inpudiy/KOMETA/IMAGE/GALLERY/blue.webp

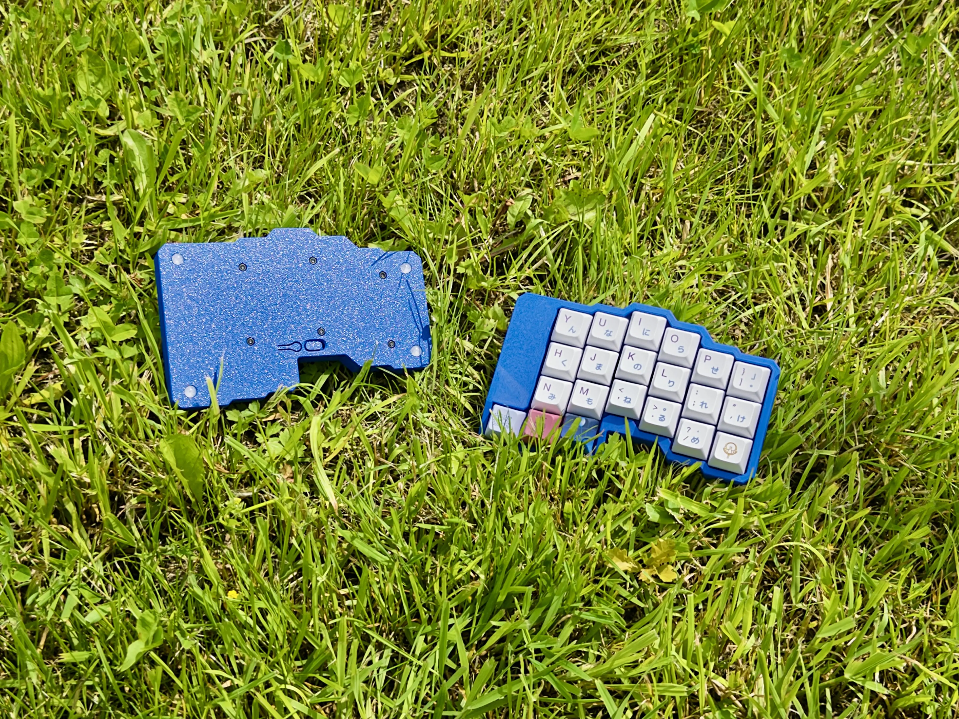
IMAGE/GALLERY/blue.webp
