inpudiy/KOMETA/IMAGE/GALLERY/green.webp

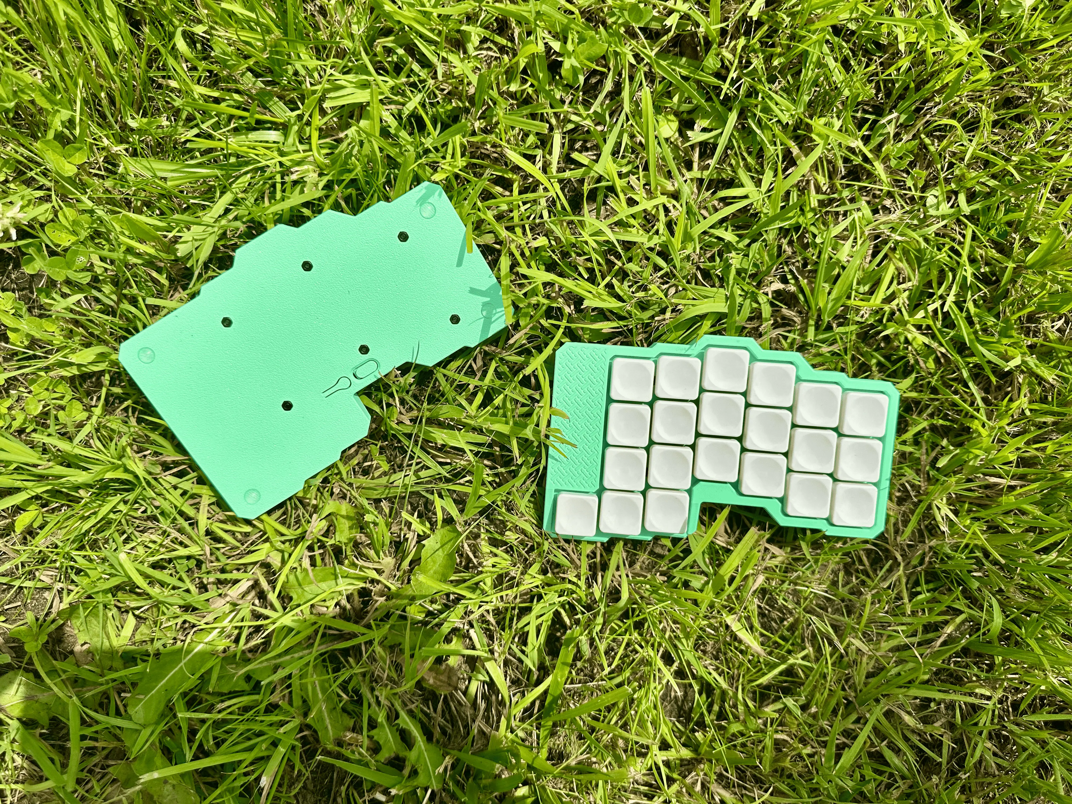
IMAGE/GALLERY/green.webp
